xyzz/xyztkl-r1/cosmetic/bottom-01.png

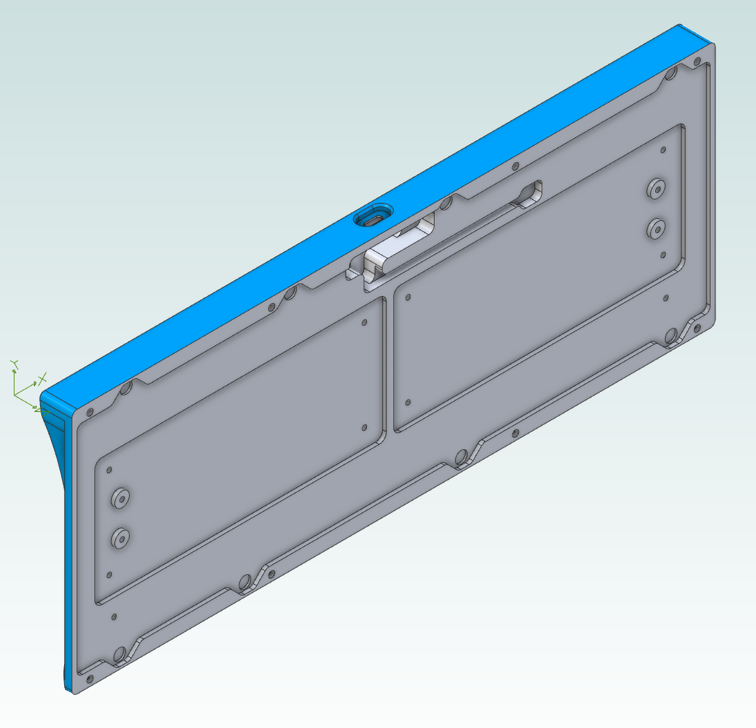
cosmetic/bottom-01.png
