xyzz/xyztkl-r1/cosmetic/bottom-02.png

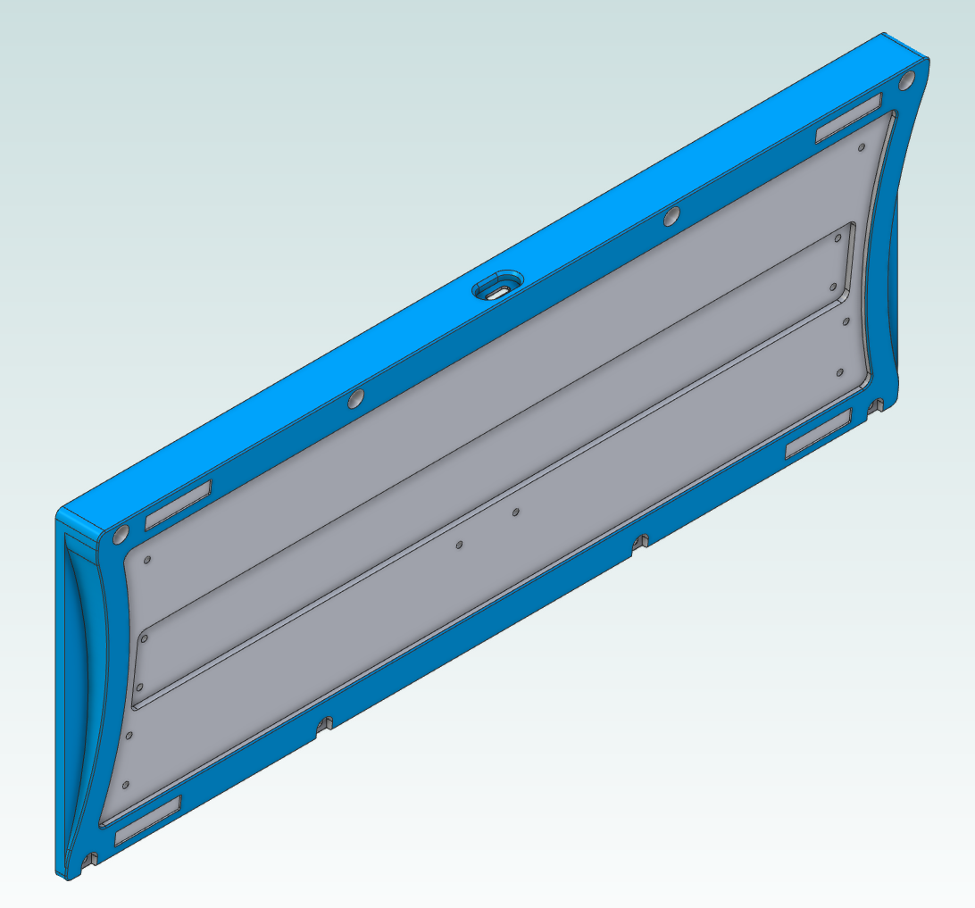
cosmetic/bottom-02.png
