xyzz/xyztkl-r1/cosmetic/cf-accent-02.png

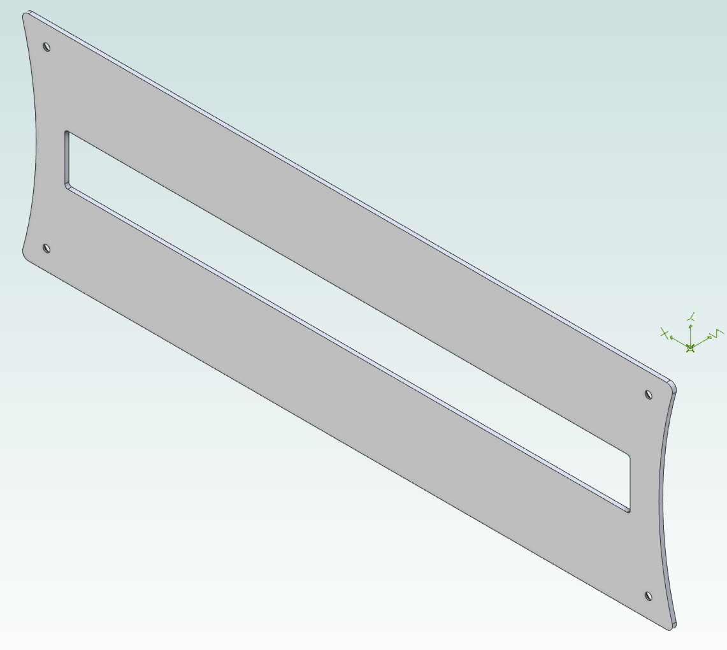
cosmetic/cf-accent-02.png
