xyzz/xyztkl-r1/cosmetic/top-01.png

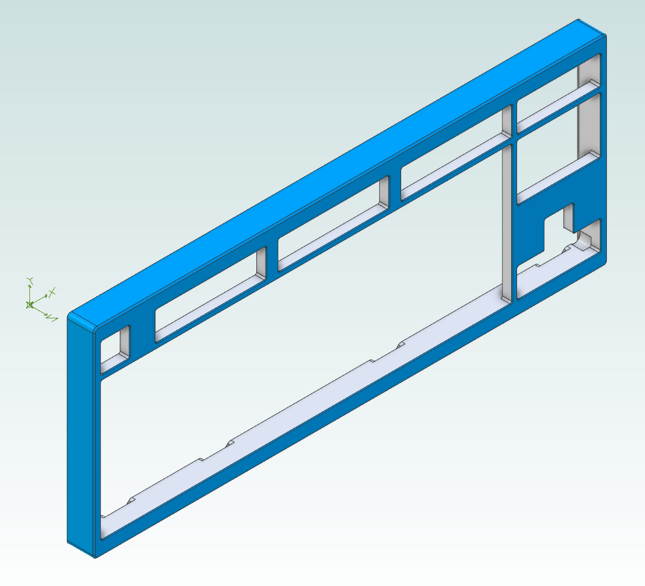
cosmetic/top-01.png
