xyzz/xyztkl-r1/cosmetic/top-02.png

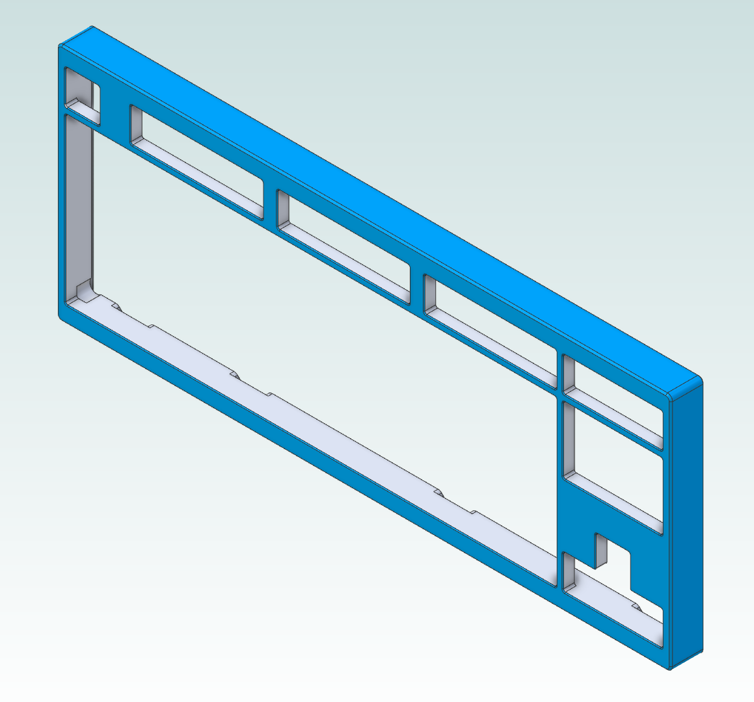
cosmetic/top-02.png
