xyzz/xyztkl-r1/cosmetic/weight-outside-02.png

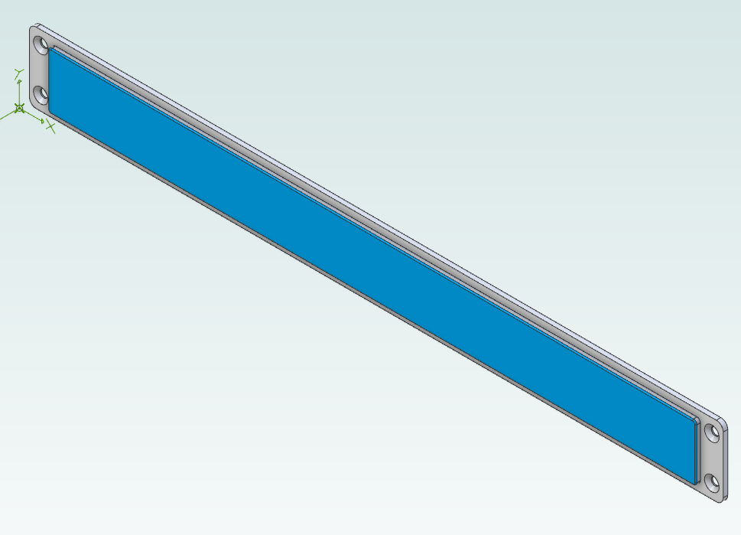
cosmetic/weight-outside-02.png
